ericpearson1313/tt_deployment_timer/test/tb.v

// vim: ts=4:
`default_nettype none
`timescale 1ns / 1ps

/* This testbench just instantiates the module and makes some convenient wires
   that can be driven / tested by the cocotb test.py.
*/
module tb ();

  // Dump the signals to a FST file. You can view it with gtkwave or surfer.
  initial begin
    $dumpfile("tb.fst");
    $dumpvars(0, tb);
    //#1;
  end

  // Wire up the inputs and outputs:
  reg clk;
  reg rst_n;
  reg ena;
  reg [7:0] ui_in;
  reg [7:0] uio_in;
  wire [7:0] uo_out;
  wire [7:0] uio_out;
  wire [7:0] uio_oe;

  // Replace tt_um_example with your module name:
	wire sda;
	wire scl;
	wire [3:0] dip_sw;
	wire cont_sense;
  	tt_um_deploy_timer user_project (
      .ui_in  ( { ui_in[7:5], cont_sense, dip_sw[3:0] } ),    // Dedicated inputs
      .uo_out (uo_out),   // Dedicated outputs
      .uio_in ( { uio_in[7:2], scl, sda } ),   // IOs: Input path
      .uio_out(uio_out),  // IOs: Output path
      .uio_oe (uio_oe),   // IOs: Enable path (active high: 0=input, 1=output)
      .ena    (ena),      // enable - goes high when design is selected
      .clk    (clk),      // clock
      .rst_n  (rst_n)     // not reset
  	);

	// connect to observe signal names, makes viewing easier

	wire sda_oe, sda_out, sda_in;
	assign sda_oe = uio_oe[0];
	assign sda_out= uio_out[0];
	assign sda_in = sda;

	wire scl_oe, scl_out, scl_in;
	assign scl_oe = uio_oe[1];
	assign scl_out= uio_out[1];
	assign scl_in = scl;

	wire cont_enable;
	assign cont_enable = uo_out[0];

	wire speaker, speaker_n, deploy, dump, charge;
	wire status_led;
	assign speaker = uo_out[1]; // active hi
	assign speaker_n=uo_out[2]; // active zero or complementary.
	assign deploy  = uo_out[3]; // active hi
	assign dump    = uo_out[4]; // active hi
	assign charge  = uo_out[5]; // active hi
	assign status_led = uo_out[6]; // active hi

	wire reset;
	assign reset = !rst_n;

	// Bus, 1 clock driver, 2 data drivers.
	wire sda_soe; // slave pulls down sda
	assign scl = ( scl_oe ) ? 1'b0 : 1'b1;
	assign sda = ( sda_oe ) ? 1'b0 : 
	             ( sda_soe ) ? 1'b0 : 1'b1;


	// Wire up an accel sim model 
	wire [11:0] x, y, z; // accell inputs into model
	accel_slave i_accel_sim (
    	.clk(clk),
    	.reset(reset),
		.en( 1'b1 ),
    	.sda( sda )     ,
    	.sda_oe( sda_soe )     ,
    	.scl( scl ) ,
    	.x( x ),
    	.y( y ),
    	.z( z )
	);

	// WIre up a accel monitor
	wire [11:0] xm, ym, zm; // accell inputs into model
	wire strobe, data_strobe;
	wire [7:0] data;
	accel_monitor i_accel_mon (
    	.clk(clk),
    	.reset(reset),
		.en( 1'b1 ),
    	.sda( sda ) ,
    	.scl( scl ) ,
		.strobe( strobe ),
    	.x( xm ),
    	.y( ym ),
    	.z( zm ),
		.data( data ),
		.data_strobe( data_strobe )
	);


dump_playback i_playback( .clk(clk), .reset(reset) );

endmodule

module dump_playback (
    input clk,
    input reset
    );
    
    wire phase, charge, dump, deploy, cont_enable, cont_sense, speaker, status_led;
    wire [11:0] xs, ys, zs;
    wire [10:0] timer;
    wire [2:0] start_cnt;
    wire [3:0] dip_sw;
    wire [1:0] empty;
    
    integer fd;
    integer ii;
    reg [63:0] mem [0:4095];
    reg [519:0] line;   // enough to hold 64 chars + newline

    initial begin
        fd = $fopen("../tools/flight_oct_3_g127.bin", "r");
        if (fd == 0) begin
            $display("ERROR: cannot open file");
            $finish;
        end
        for( ii = 0; ii < 4096; ii = ii + 1 ) begin
            void'($fgets(line, fd));
            void'($sscanf(line, "%b", mem[ii])); 
        end
        $fclose(fd);
    end

    logic [11:0] mem_cnt;
    always @(posedge clk) 
        mem_cnt <= ( reset ) ? 0 : ( mem_cnt < 4095 ) ? mem_cnt + 1 : mem_cnt; 

    assign { phase, charge, dump, deploy, cont_enable, cont_sense, speaker, status_led, 
             xs[11:0], ys[11:0], zs[11:0],dip_sw[3:0], timer[7:0],timer[10:8], start_cnt[2:0], empty[1:0] } = mem[mem_cnt];


endmodule
